deadsy/wallaby_cad/cad/head_cover_scaled.dxf

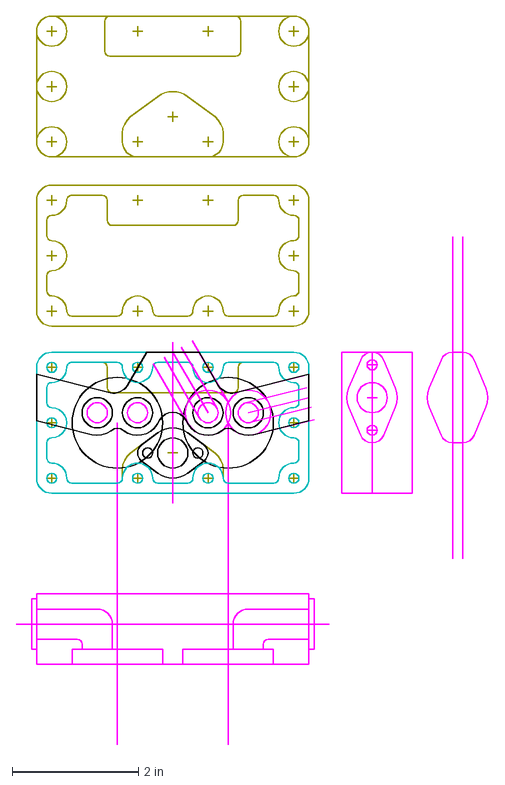
[picture p16: CAD file, 2015-06-26]
cad/head_cover_scaled.dxf
7.48 x 11.5 in
