deadsy/wallaby_cad/cad/piston_scaled.dxf

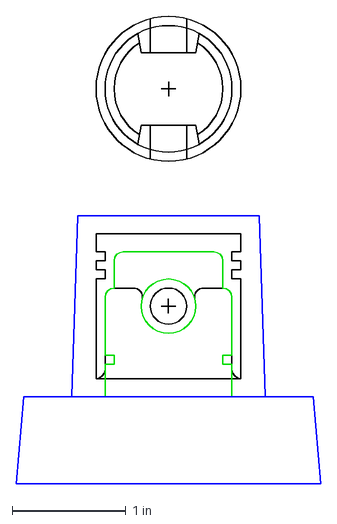
[picture p17: CAD file, 2014-12-14]
cad/piston_scaled.dxf
2.69 x 4.12 in
