deadsy/wallaby_cad/cad/piston.dxf

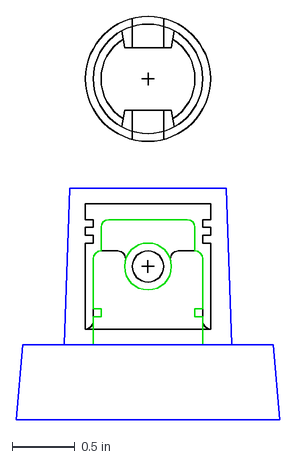
[picture p18: CAD file, 2014-12-14]
cad/piston.dxf
2.10 x 3.23 in
