deadsy/wallaby_cad/cad/inlet_stub.dxf

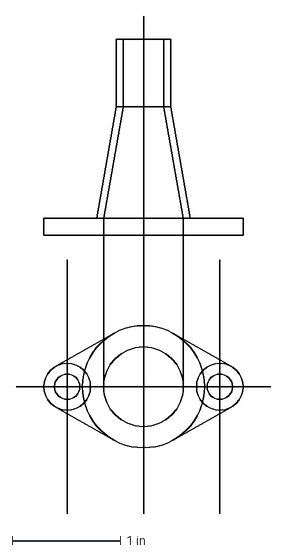
[picture p19: CAD file, 2014-11-18]
cad/inlet_stub.dxf
2.35 x 4.60 in
