deadsy/wallaby_cad/cad/inlet_stub_scaled.dxf

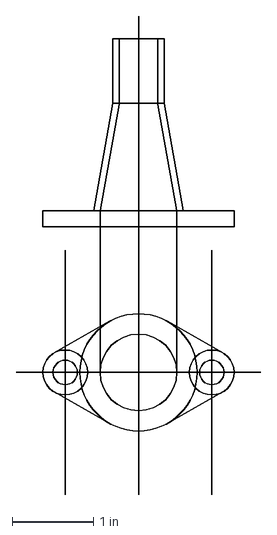
[picture p20: CAD file, 2014-11-18]
cad/inlet_stub_scaled.dxf
3.00 x 5.87 in
