deadsy/wallaby_cad/cad/rocker_bearing_scaled.dxf

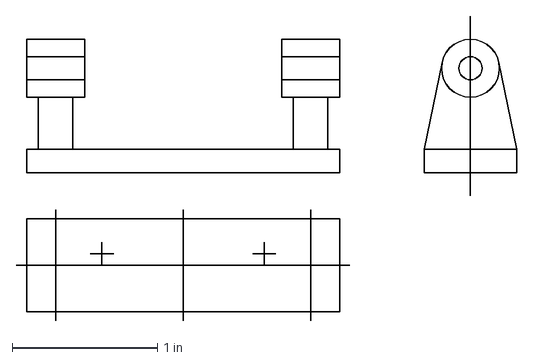
[picture p21: CAD file, 2014-11-11]
cad/rocker_bearing_scaled.dxf
3.45 x 2.10 in
