deadsy/wallaby_cad/cad/rocker_bearing.dxf

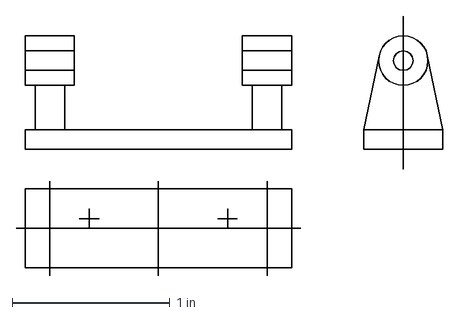
[picture p22: CAD file, 2014-11-11]
cad/rocker_bearing.dxf
2.70 x 1.64 in
