deadsy/wallaby_cad/cad/conrod_scaled.dxf

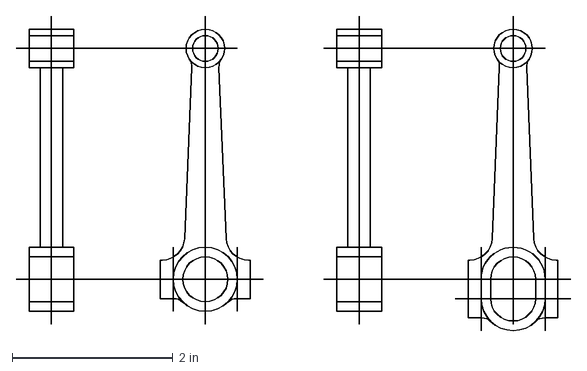
[picture p23: CAD file, 2014-11-11]
cad/conrod_scaled.dxf
6.90 x 3.91 in
