deadsy/wallaby_cad/cad/bearing_cap_scaled.dxf

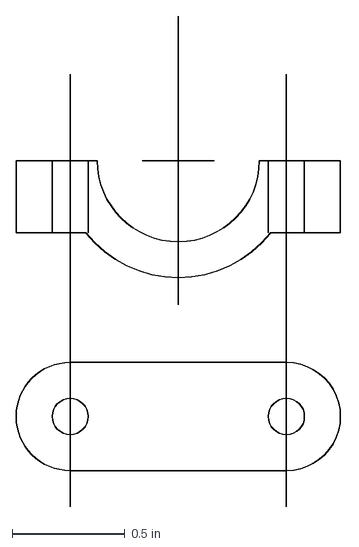
[picture p24: CAD file, 2014-11-09]
cad/bearing_cap_scaled.dxf
1.45 x 2.17 in
