deadsy/wallaby_cad/cad/balance_weight_scaled.dxf

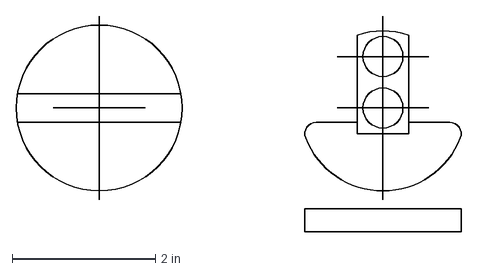
[picture p25: CAD file, 2014-11-09]
cad/balance_weight_scaled.dxf
6.21 x 3.00 in
