deadsy/wallaby_cad/cad/flywheel_scaled.dxf

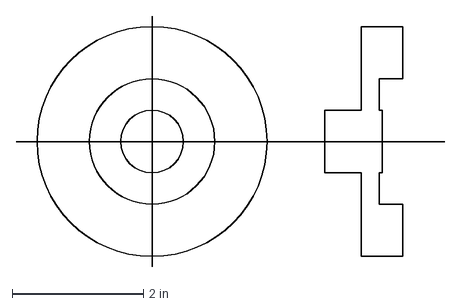
[picture p26: CAD file, 2014-11-09]
cad/flywheel_scaled.dxf
6.54 x 3.83 in
