deadsy/wallaby_cad/cad/oil_pump_housing_scaled.dxf

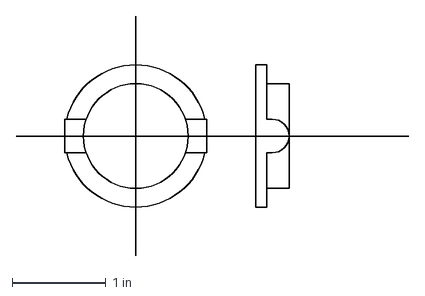
[picture p27: CAD file, 2014-11-09]
cad/oil_pump_housing_scaled.dxf
4.19 x 2.55 in
