deadsy/wallaby_cad/cad/conrod.dxf

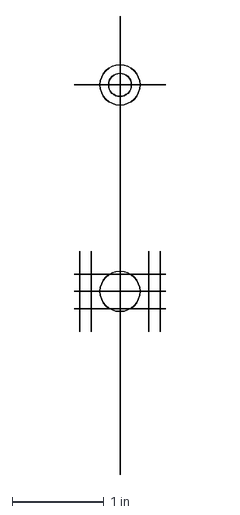
[picture p28: CAD file, 2014-11-08]
cad/conrod.dxf
1.00 x 5.00 in
