deadsy/wallaby_cad/cad/balance_weight.dxf

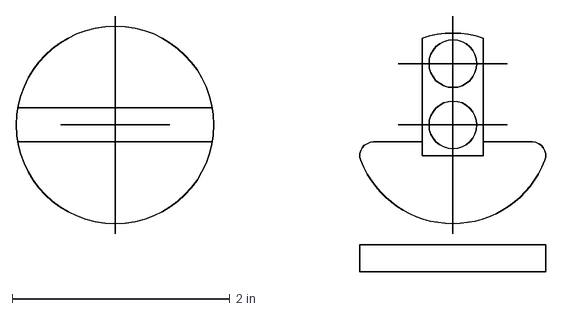
[picture p29: CAD file, 2014-11-07]
cad/balance_weight.dxf
4.87 x 2.35 in
