deadsy/wallaby_cad/cad/oil_pump_housing.dxf

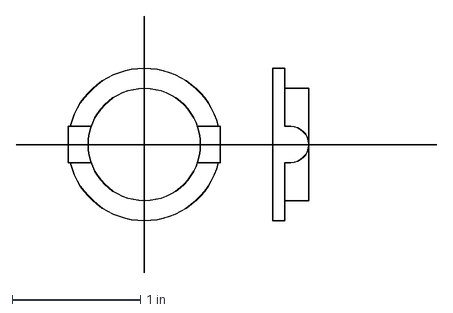
[picture p30: CAD file, 2014-11-06]
cad/oil_pump_housing.dxf
3.28 x 2.00 in
