deadsy/wallaby_cad/cad/bearing_cap.dxf

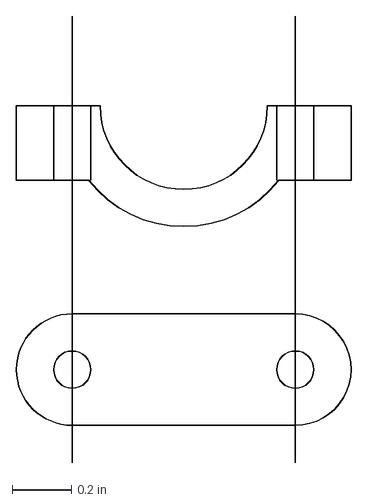
[picture p31: CAD file, 2014-11-06]
cad/bearing_cap.dxf
1.13 x 1.50 in
