deadsy/wallaby_cad/cad/flywheel.dxf

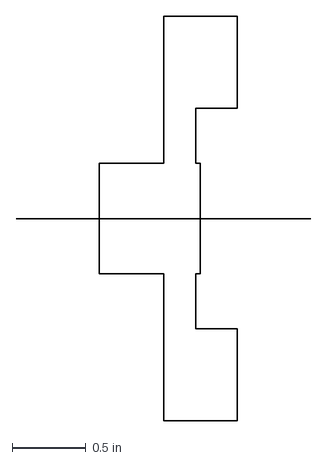
[picture p32: CAD file, 2014-11-05]
cad/flywheel.dxf
2.00 x 2.75 in
