deadsy/wallaby_cad/cad/engine_body_scaled.dxf

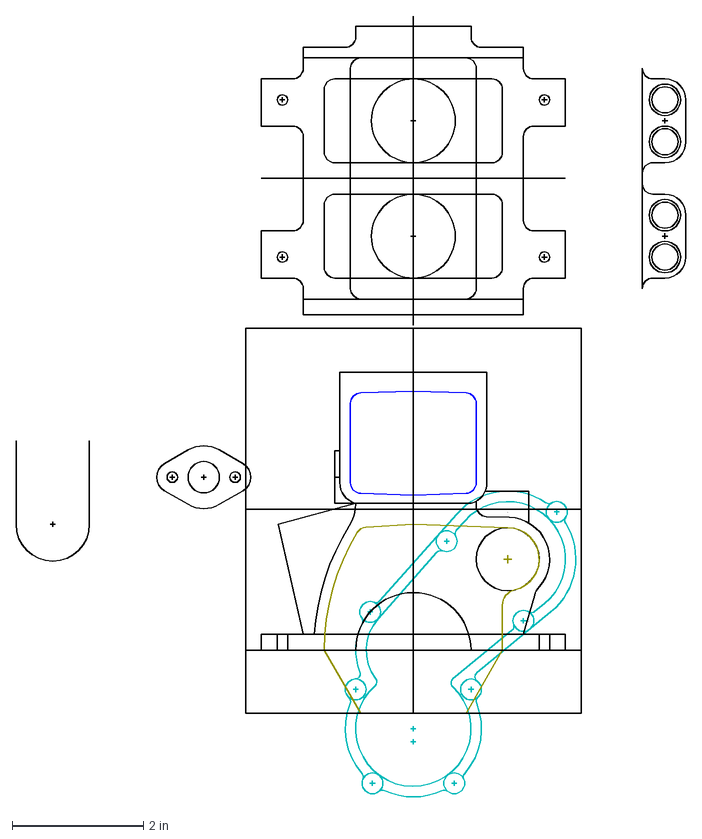
[picture p33: CAD file, 2014-11-05]
cad/engine_body_scaled.dxf
10.2 x 11.9 in
