deadsy/wallaby_cad/cad/engine_body_outline.dxf

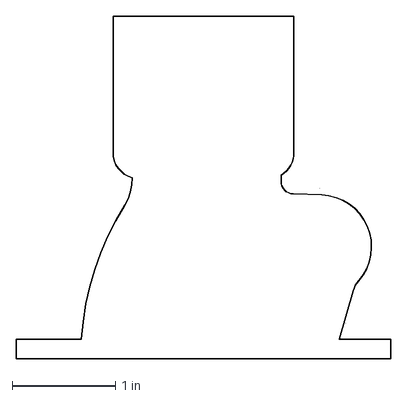
[picture p34: CAD file, 2014-10-24]
cad/engine_body_outline.dxf
3.62 x 3.31 in
