deadsy/wallaby_cad/cad/timing_cover_scaled.dxf

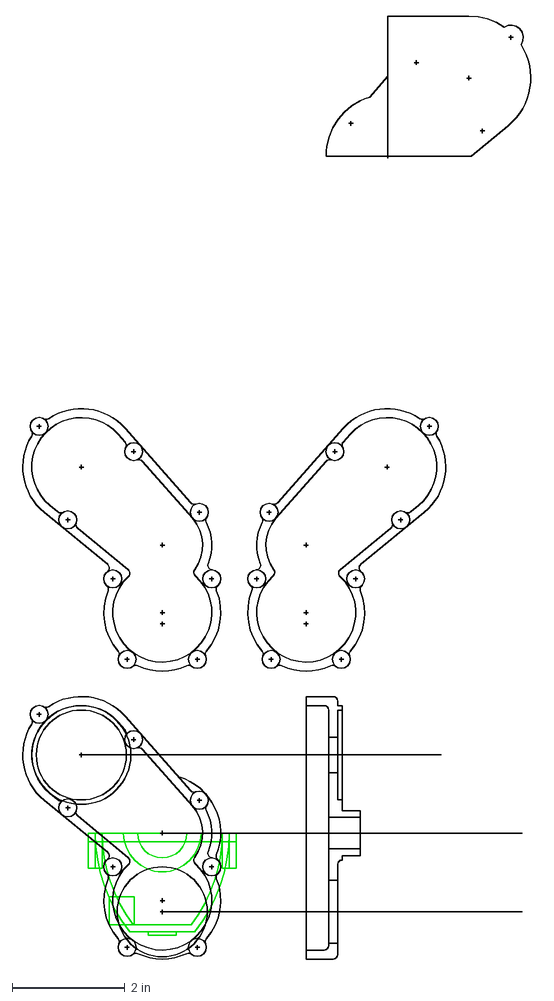
[picture p35: CAD file, 2014-10-22]
cad/timing_cover_scaled.dxf
9.25 x 16.7 in
