deadsy/wallaby_cad/cad/timing_cover.dxf

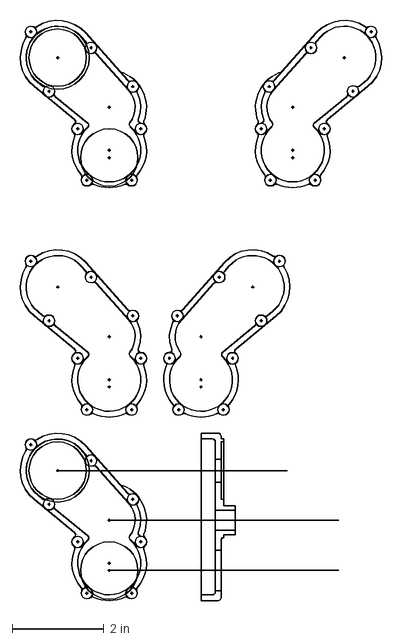
[picture p36: CAD file, 2014-10-22]
cad/timing_cover.dxf
8.06 x 12.8 in
