deadsy/wallaby_cad/cad/sump_scaled.dxf

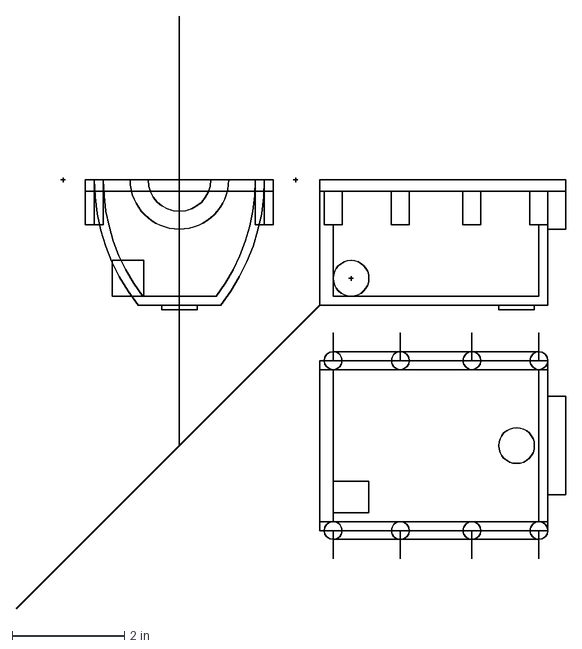
[picture p37: CAD file, 2014-10-22]
cad/sump_scaled.dxf
9.80 x 10.6 in
