deadsy/wallaby_cad/cad/sump.dxf

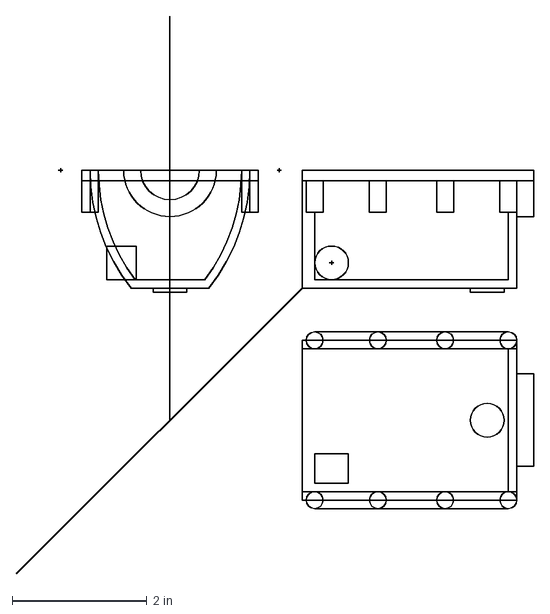
[picture p38: CAD file, 2014-10-22]
cad/sump.dxf
7.68 x 8.28 in
